gsyan888/MusicBoxCustomCylinder/images/3dp-music-box-custom-cylinder-6.jpg

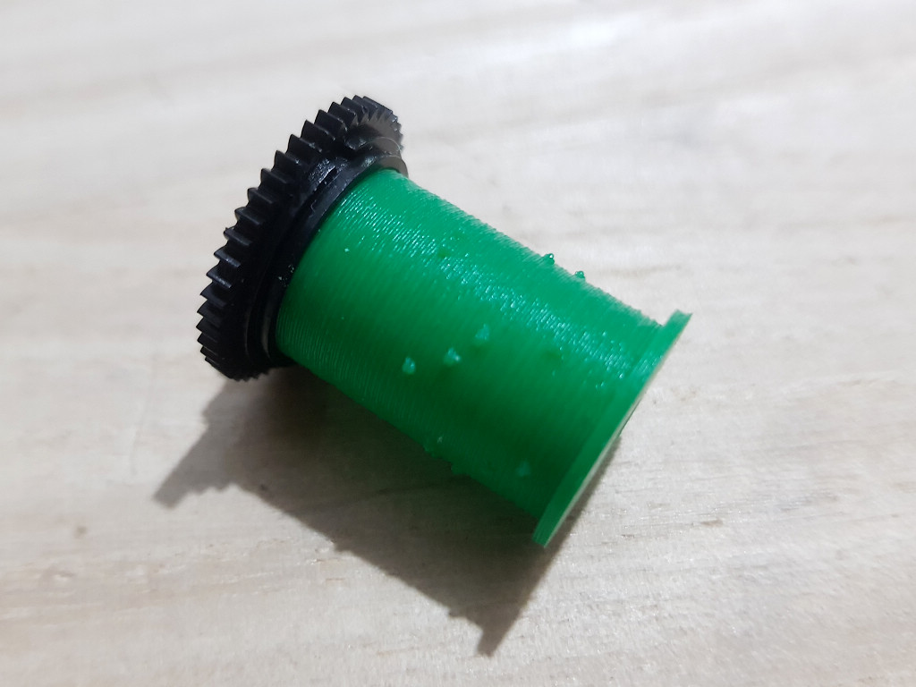
images/3dp-music-box-custom-cylinder-6.jpg
